Lefix2/pixfrog/docs/img/og-cover.png

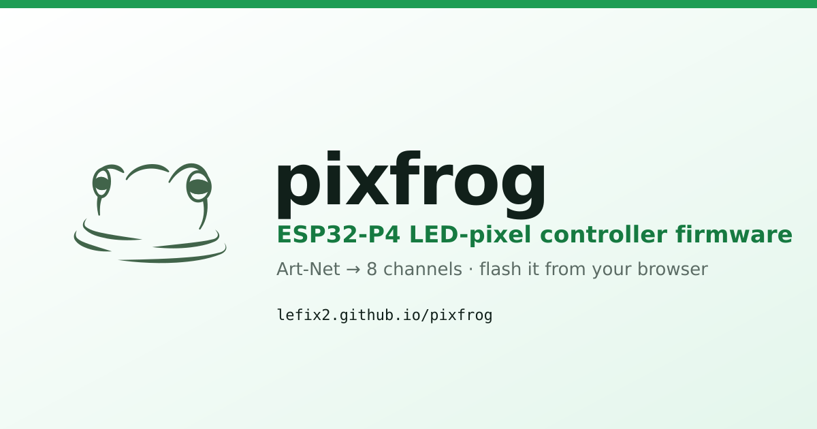
docs/img/og-cover.png
