Lefix2/pixfrog/docs/img/rack-closeup.jpg

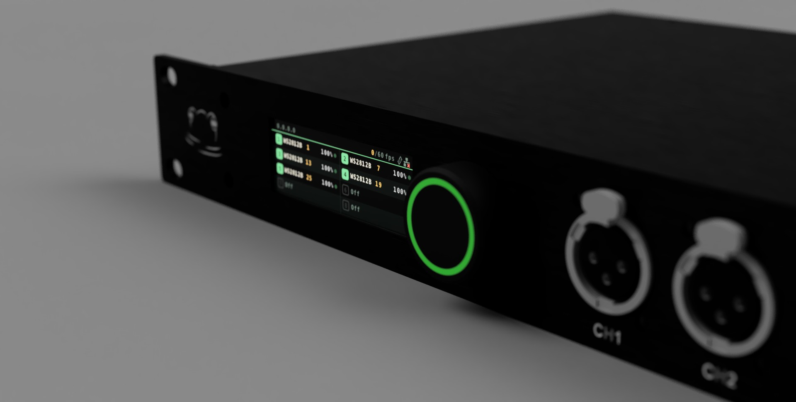
docs/img/rack-closeup.jpg
