Lefix2/pixfrog/docs/img/web-dashboard-fr.png

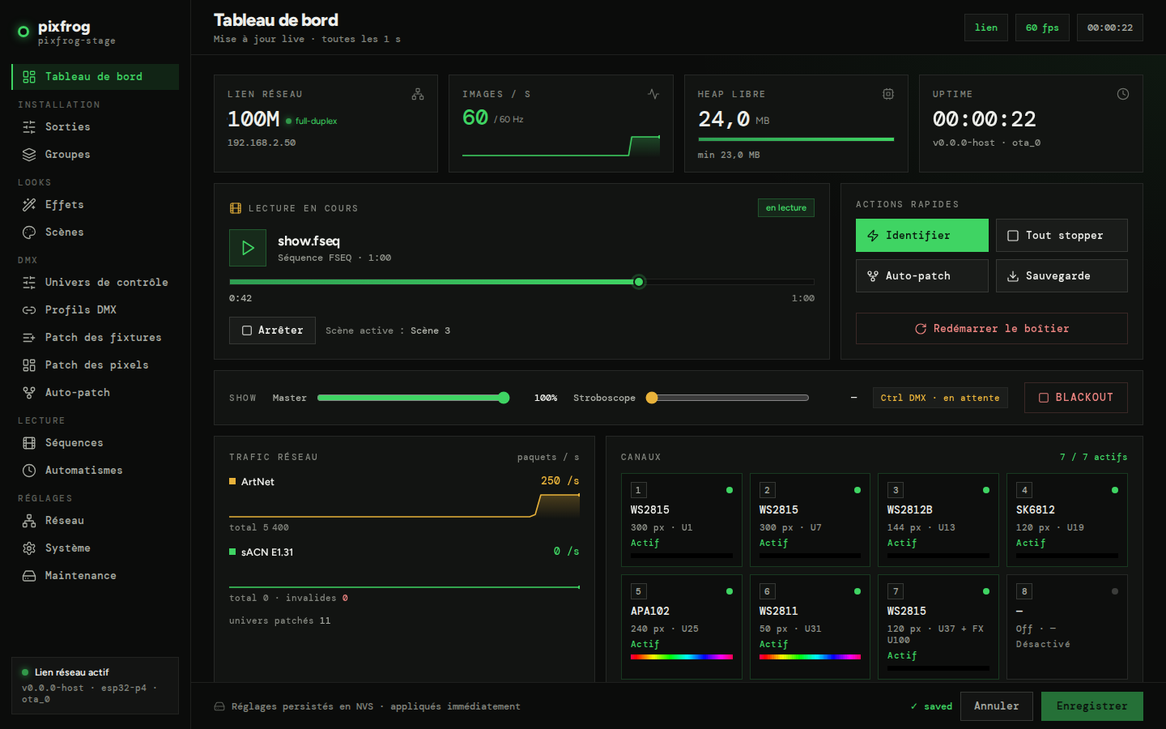
docs/img/web-dashboard-fr.png
