Lefix2/pixfrog/docs/img/web-scenes-fr.png

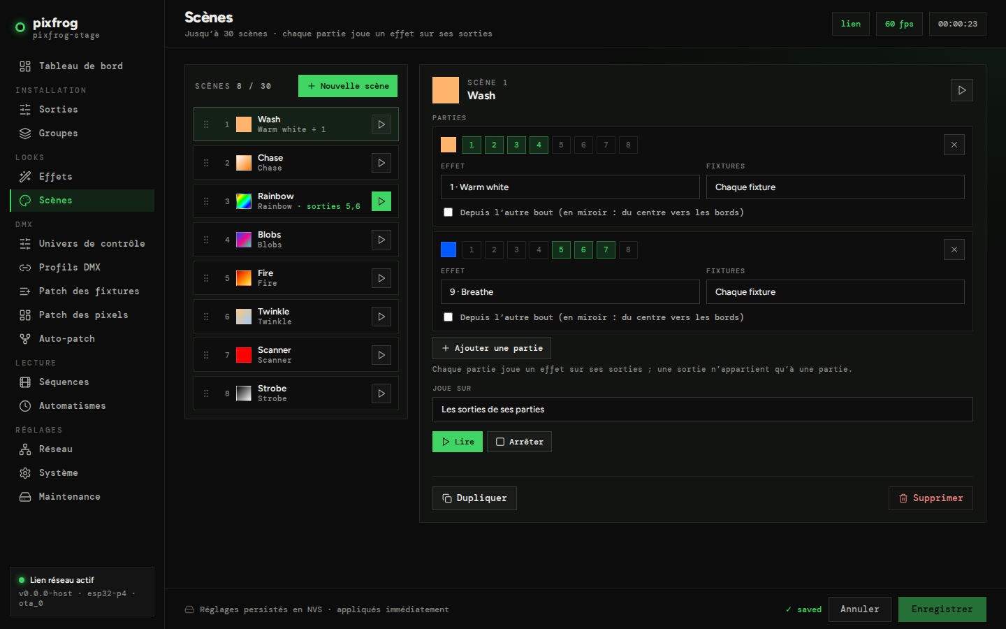
docs/img/web-scenes-fr.png
