Lefix2/pixfrog/tools/emulator/golden/nv3007/channel1.png

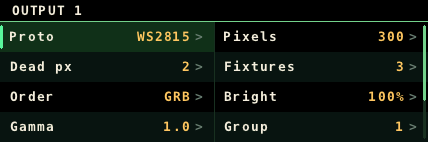
tools/emulator/golden/nv3007/channel1.png
