Lefix2/pixfrog/tools/emulator/golden/nv3007/channel1_dead_px.png

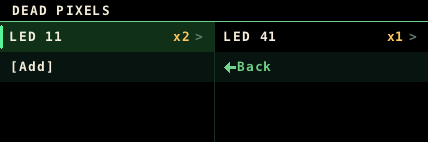
tools/emulator/golden/nv3007/channel1_dead_px.png
