Lefix2/pixfrog/tools/emulator/golden/nv3007/channel1_fixture2.png

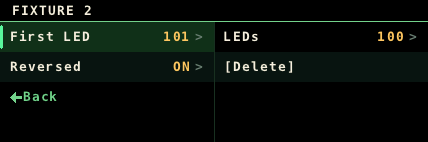
tools/emulator/golden/nv3007/channel1_fixture2.png
