Lefix2/pixfrog/tools/emulator/golden/nv3007/channel1_fixtures.png

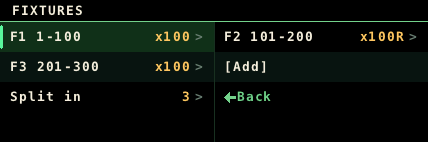
tools/emulator/golden/nv3007/channel1_fixtures.png
