Lefix2/pixfrog/tools/emulator/golden/nv3007/control_menu.png

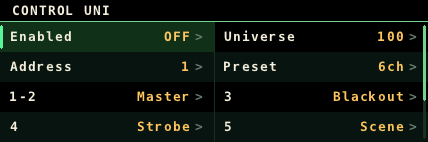
tools/emulator/golden/nv3007/control_menu.png
