Lefix2/pixfrog/tools/emulator/golden/nv3007/dmx_menu.png

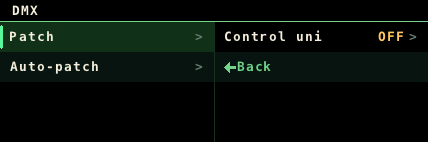
tools/emulator/golden/nv3007/dmx_menu.png
