Lefix2/pixfrog/tools/emulator/golden/nv3007/main_menu.png

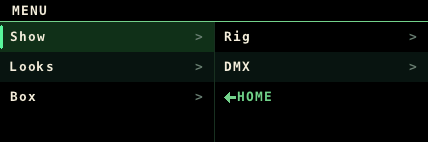
tools/emulator/golden/nv3007/main_menu.png
