Lefix2/pixfrog/tools/emulator/golden/nv3007/output_patch1.png

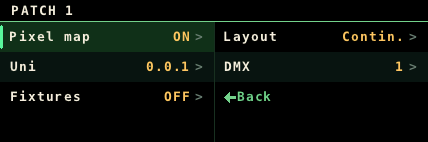
tools/emulator/golden/nv3007/output_patch1.png
