Lefix2/pixfrog/tools/emulator/golden/nv3007/output_patch2.png

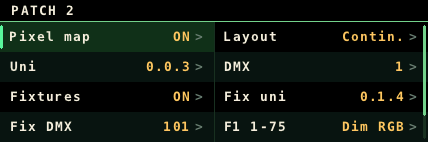
tools/emulator/golden/nv3007/output_patch2.png
