Lefix2/pixfrog/tools/emulator/golden/nv3007/patch_list.png

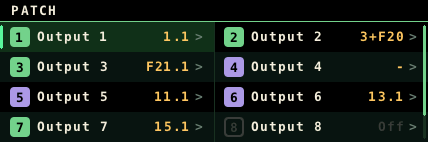
tools/emulator/golden/nv3007/patch_list.png
