Lefix2/pixfrog/tools/emulator/golden/nv3007/rig_menu.png

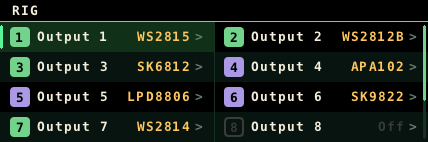
tools/emulator/golden/nv3007/rig_menu.png
