Lefix2/pixfrog/tools/emulator/golden/nv3007/scene_edit.png

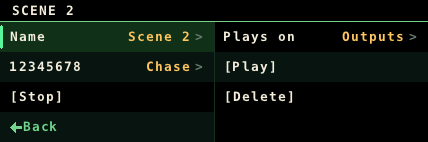
tools/emulator/golden/nv3007/scene_edit.png
