Lefix2/pixfrog/tools/emulator/golden/nv3007/scene_part.png

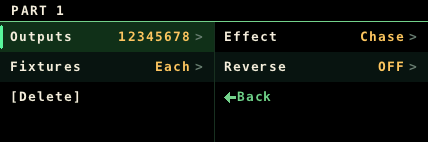
tools/emulator/golden/nv3007/scene_part.png
