Lefix2/pixfrog/tools/emulator/golden/nv3007/scenes_menu.png

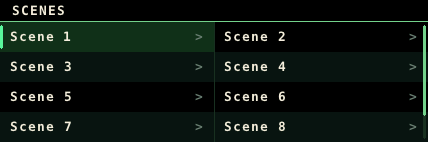
tools/emulator/golden/nv3007/scenes_menu.png
