Lefix2/pixfrog/tools/emulator/golden/nv3007/show_menu.png

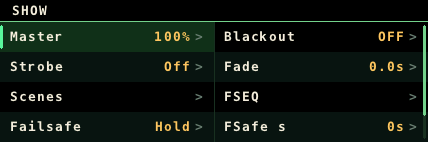
tools/emulator/golden/nv3007/show_menu.png
