Lefix2/pixfrog/tools/emulator/golden/st7789/channel1.png

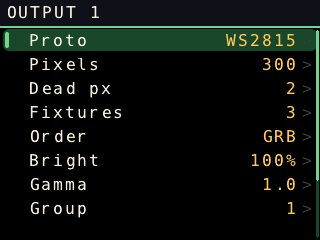
tools/emulator/golden/st7789/channel1.png
