Lefix2/pixfrog/tools/emulator/golden/st7789/channel1_dead_px.png

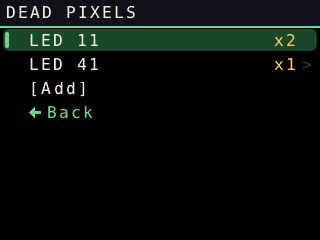
tools/emulator/golden/st7789/channel1_dead_px.png
