Lefix2/pixfrog/tools/emulator/golden/st7789/channel1_fixture2.png

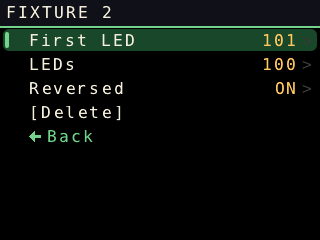
tools/emulator/golden/st7789/channel1_fixture2.png
