Lefix2/pixfrog/tools/emulator/golden/st7789/channel1_fixtures.png

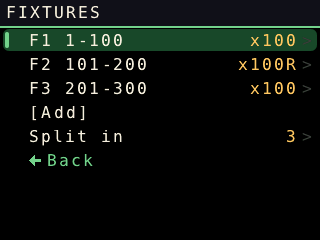
tools/emulator/golden/st7789/channel1_fixtures.png
