Lefix2/pixfrog/tools/emulator/golden/st7789/control_menu.png

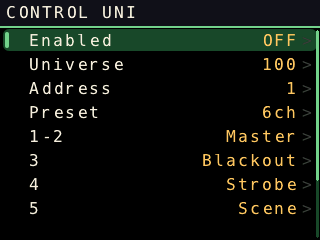
tools/emulator/golden/st7789/control_menu.png
