Lefix2/pixfrog/tools/emulator/golden/st7789/main_menu.png

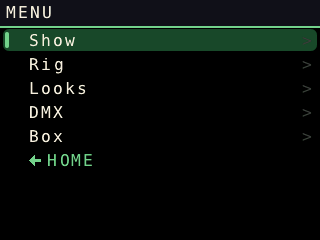
tools/emulator/golden/st7789/main_menu.png
