Lefix2/pixfrog/tools/emulator/golden/st7789/output_patch1.png

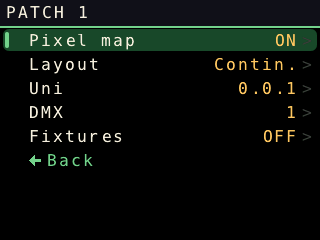
tools/emulator/golden/st7789/output_patch1.png
