Lefix2/pixfrog/tools/emulator/golden/st7789/output_patch2.png

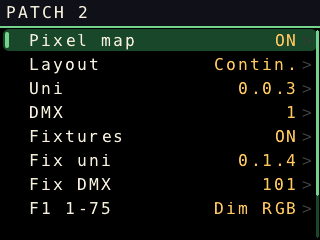
tools/emulator/golden/st7789/output_patch2.png
