Lefix2/pixfrog/tools/emulator/golden/st7789/patch_list.png

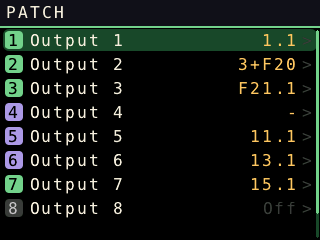
tools/emulator/golden/st7789/patch_list.png
