Lefix2/pixfrog/tools/emulator/golden/st7789/rig_menu.png

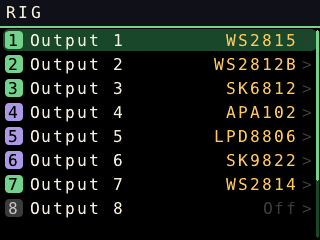
tools/emulator/golden/st7789/rig_menu.png
