Lefix2/pixfrog/tools/emulator/golden/st7789/scene_edit.png

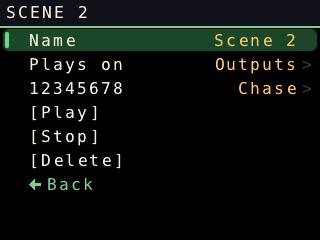
tools/emulator/golden/st7789/scene_edit.png
