Lefix2/pixfrog/tools/emulator/golden/st7789/scene_part.png

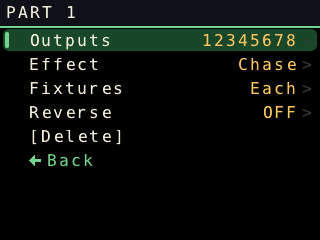
tools/emulator/golden/st7789/scene_part.png
