Lefix2/pixfrog/tools/emulator/golden/st7789/scenes_menu.png

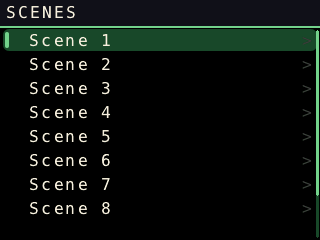
tools/emulator/golden/st7789/scenes_menu.png
