Lefix2/pixfrog/tools/emulator/golden/st7789/show_menu.png

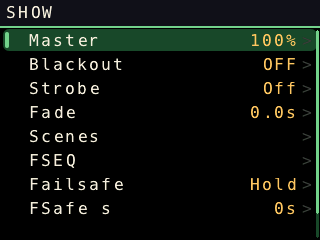
tools/emulator/golden/st7789/show_menu.png
