Lefix2/pixfrog/boards/esp32_p4_devkit.h

// Board definition: Waveshare ESP32-P4 Module DEV-KIT
// (datasheet:
// https://www.espressif.com/sites/default/files/documentation/esp32-p4_datasheet_en.pdf)
//
// Pinout source: Waveshare ESP32-P4 Module DEV-KIT schematic (P6 40-pin header).
// Only GPIOs exposed on P6 are candidates here.
//
// ════════════════════════════════════════════════════════════════════════════
// P6  —  40-pin 2.54 mm header (even = left row, odd = right row)
// ════════════════════════════════════════════════════════════════════════════
//
//   Pin  Left              │  Pin  Right
//   ──────────────────────────────────────
//    2   GPIO7  (I2C SDA)  │   1   VCC_5V
//    4   GPIO8  (I2C SCL)  │   3   GND
//    6   GPIO23 (LED CH3 CLK) │ 5  GPIO37  (UART0 TXD)
//    8   GND               │   7   GPIO38  (UART0 RXD)
//   10   GPIO21 (TFT DC)   │   9   GPIO22  (LED CH3 DATA)
//   12   —                 │  11   GND
//   14   GPIO6  (TFT MOSI) │  13   GPIO5   (LED CH2 CLK)
//   16   —                 │  15   GPIO4   (LED CH2 DATA)
//   18   —                 │  17   GND
//   20   GPIO3  (LED CH1 CLK) │ 19  GPIO1  (status LED)
//   22   GPIO2  (LED CH1 DATA) │ 21  GPIO36 (strapping — keep HIGH)
//   24   GPIO0  (TFT CLK)  │  23   GPIO32  (LED CH6 DATA)
//   26   GND               │  25   GPIO25  (LED CH4 CLK)
//   28   GPIO24 (LED CH4 DATA) │ 27  GND
//   30   GPIO33 (LED CH6 CLK) │ 29  GPIO54  (LED CH8 CLK)
//   32   GPIO26 (LED CH5 DATA) │ 31  GND
//   34   GPIO48 (LED CH7 CLK) │ 33  GPIO46  (LED CH5 CLK)
//   36   GPIO53 (LED CH8 DATA) │ 35  GPIO27  (TFT RST)
//   38   GPIO47 (LED CH7 DATA) │ 37  GPIO45  (TFT backlight)
//   40   GND               │  39   —
//
// ════════════════════════════════════════════════════════════════════════════
// On-board peripheral  →  GPIO usage
// ════════════════════════════════════════════════════════════════════════════
//
//  LED bus (LCD_CAM 16-bit parallel, 16 MHz PCLK)
//    CH1 DATA/CLK : GPIO2  / GPIO3
//    CH2 DATA/CLK : GPIO4  / GPIO5
//    CH3 DATA/CLK : GPIO22 / GPIO23
//    CH4 DATA/CLK : GPIO24 / GPIO25
//    CH5 DATA/CLK : GPIO26 / GPIO46
//    CH6 DATA/CLK : GPIO32 / GPIO33
//    CH7 DATA/CLK : GPIO47 / GPIO48
//    CH8 DATA/CLK : GPIO53 / GPIO54
//
//  I2C shared bus (OLED SSD1306 + seesaw encoder)
//    SDA : GPIO7    SCL : GPIO8
//
//  SPI display (ST7789V / ILI9341) — on the shield's J13 break-out header
//    CLK  : GPIO0    MOSI : GPIO6
//    CS   : GPIO20   DC   : GPIO21
//    RST  : GPIO27
//
//  Status LED         : GPIO1
//  UART0 console      : TX=GPIO37  RX=GPIO38
//
//  Ethernet RMII (IP101GR PHY, fixed SoC pins — not on P6)
//    TXD0=34  TXD1=35  TX_EN=49  RXD0=29  RXD1=30  CRS_DV=28  REF_CLK=50
//    MDC=31   MDIO=52  PHY_RESET=51
//
//  ES8311 audio codec + NS4150B speaker amp (on-board, not on J13)
//    MCLK=GPIO13  SCLK=GPIO12  LRCK=GPIO10  ASDOUT(codec→P4)=GPIO11
//    DSDIN(P4→codec)=GPIO9. Config via the shared I2C bus above (0x18).
//    Amp enable PA_CTRL: R52 removed, 10 kΩ pull-up to 3.3 V (GPIO53 is
//    LED CH8 DATA only).
//
// ════════════════════════════════════════════════════════════════════════════
// Strapping pins (ESP32-P4 datasheet §3.3)
// ════════════════════════════════════════════════════════════════════════════
//
//  GPIO35 — boot/download select (driven by BOOT button, not on P6)
//  GPIO36 — must read HIGH for reliable serial-download boot
//  GPIO34 — JTAG source select at boot
//
// GPIO matrix: every peripheral signal is routed through the GPIO matrix,
// so any free GPIO is a valid LCD_CAM data line or SPI pin. The only
// hard constraints are the strapping pins above and the fixed RMII pins.

#pragma once

#include <stdint.h>

namespace pixfrog::board {

// ────────────────────────────────────────────────────────────────────────────
// Identification
// ────────────────────────────────────────────────────────────────────────────

constexpr const char* kBoardName = "esp32_p4_devkit";
constexpr const char* kBoardRev  = "v0";

// ────────────────────────────────────────────────────────────────────────────
// LCD_CAM 16-bit parallel — DATA[k] and CLOCK[k] for 8 LED channels
// ────────────────────────────────────────────────────────────────────────────
//
// Bit position on the parallel bus → physical GPIO.
// Bit 0 = CH1 DATA, Bit 1 = CH1 CLOCK, Bit 2 = CH2 DATA, etc.
//
// Pad power domains (P4 datasheet §2, Waveshare module wiring):
//   GPIO 2-25   VDD_IO_0/4 ← 3.3 V direct
//   GPIO 39-48  VDD_IO_5   ← internal LDO VO4 — MUST be programmed to 3.3 V
//               at boot (main::power_vdd_io5_pads), else outputs swing ~1.2 V.
//               Covers CH5 CLOCK (46) and CH7 DATA/CLOCK (47/48).
//   GPIO 49-54  VDD_IO_6   ← 3.3 V direct

constexpr int kLedDataGpio[8]  = { 2, 4, 22, 24, 26, 32, 47, 53 };
constexpr int kLedClockGpio[8] = { 3, 5, 23, 25, 46, 33, 48, 54 };

// Full 16-pin bus in bit order (DATA0, CLK0, DATA1, CLK1, ...).
// clang-format off
constexpr int kLedBusGpio[16] = {
     2,  3,   4,  5,  22, 23,  24, 25,
    26, 46,  32, 33,  47, 48,  53, 54,
};
// clang-format on

// ────────────────────────────────────────────────────────────────────────────
// Ethernet — RMII to on-board IP101GRI PHY
// ────────────────────────────────────────────────────────────────────────────
//
// Verified against the Waveshare DEV-KIT schematic (PHY U7 = IP101GRI) and
// the official board pinout. The PHY's RMII + management pins use fixed SoC
// GPIOs (28-35, 49-52) and PHY RESET is GPIO51; none are on the P6 header,
// so they do not constrain the LED pinout above.
//
// RMII data/clock equal the ESP32-P4 ETH_ESP32_EMAC_DEFAULT_CONFIG() defaults
// (IDF v5.5), so main/init_network() only has to override MDC/MDIO:
//   TXD0=34  TXD1=35  TX_EN=49  RXD0=29  RXD1=30  CRS_DV=28  REF_CLK(50M)=50
//
// Management bus + reset are read straight off U7:
//   MDC = pin 22, MDIO = pin 23, RESET = pin 32.

constexpr int kEthMdcGpio      = 31;
constexpr int kEthMdioGpio     = 52;
constexpr int kEthPhyResetGpio = 51;    // drive HIGH to release U7 from reset
constexpr int kEthPhyAddress   = 0x01;  // IP101GRI strap (AD0/AD3); verify if link fails

// ────────────────────────────────────────────────────────────────────────────
// I2C — shared bus for OLED + seesaw encoder
// ────────────────────────────────────────────────────────────────────────────

constexpr int kI2cPort        = 0;
constexpr int kI2cSdaGpio     = 7;  // header pin SDA(GPIO7)
constexpr int kI2cSclGpio     = 8;  // header pin SCL(GPIO8)
constexpr uint32_t kI2cFreqHz = 400'000;

constexpr uint8_t kOledI2cAddr    = 0x3C;
constexpr uint8_t kEncoderI2cAddr = 0x36;  // Adafruit seesaw 4991 default
// Encoder INT_N is deliberately not wired: the firmware time-polls the seesaw
// at ~30 Hz, so a 4-wire I2C harness (VCC/GND/SDA/SCL) is sufficient and
// GPIO 21 stays free.

// ────────────────────────────────────────────────────────────────────────────
// SPI display — ST7789V or ILI9341
// ────────────────────────────────────────────────────────────────────────────
//
// Routed to the shield's J13 break-out header. The ES8311 codec I2S pins
// (GPIO9-13) the display used to share are NOT exposed on J13, so the SPI
// display moved to the free, 3.3 V-direct, non-strapping GPIOs available
// there: 0/6/20/21/27. J13 also exposes GPIO36 (now the backlight, below) and
// GPIO45, which is NOT free: it gates the microSD supply (see kSdPowerGpio).
// SPI2 (HSPI) is used; every signal is routed through the GPIO matrix so any
// free GPIO is valid.

constexpr int kDisplaySpiHost  = 1;  // SPI2 / HSPI
constexpr int kDisplayClkGpio  = 0;
constexpr int kDisplayMosiGpio = 6;
constexpr int kDisplayCsGpio   = 20;
constexpr int kDisplayDcGpio   = 21;
constexpr int kDisplayRstGpio  = 27;
// 20 MHz: the P4's default SPI clock source can't derive 40 MHz cleanly
// (spi_bus_add_device → "invalid sclk speed"); 20 MHz is a clean divisor and
// well within the GPIO-matrix routing limit. Plenty for the 320×240 panel.
constexpr uint32_t kDisplaySpiFreqHz = 20'000'000;

// Backlight enable (LEDC PWM), on J13's GPIO36. Off from boot, raised only
// once the first UI frame has been pushed, so the panel never shows its white
// power-on state. -1 disables backlight control (BL hard-wired on).
// GPIO36 is a boot strapping pin, but the boot mode is decided by GPIO35 (the
// BOOT button, pulled high: flash boot); GPIO36 only matters with BOOT held,
// for the download modes. It was on GPIO45 until the microSD showed that pin
// gates the card supply: lighting the panel switched the card off.
constexpr int kDisplayBacklightGpio = 36;

// ────────────────────────────────────────────────────────────────────────────
// Miscellaneous
// ────────────────────────────────────────────────────────────────────────────

// ────────────────────────────────────────────────────────────────────────────
// microSD — SDMMC 4-bit (GPIO39-44, VDD_IO_5 domain = LDO VO4 @ 3.3 V)
// ────────────────────────────────────────────────────────────────────────────
//
// GPIO39-44 are in the VDD_IO_5 pad domain, powered by the same LDO VO4
// that is programmed to 3.3 V by power_vdd_io5_pads() at boot.
// None of these GPIOs appear in the LED bus, SPI display, I2C, ETH, or UART
// pin lists, so they are freely available for the SD slot.

// Per the DEV-KIT schematic (MicroSD block, TF slot SD1): the data lines do
// not follow the GPIO order — D0/D1 are 39/40, D2/D3 41/42, CLK 43, CMD 44.
// (The previous 39..44 = CLK, CMD, D0..D3 mapping never reached a card.)
constexpr int kSdmmcClkGpio = 43;
constexpr int kSdmmcCmdGpio = 44;
constexpr int kSdmmcD0Gpio  = 39;
constexpr int kSdmmcD1Gpio  = 40;
constexpr int kSdmmcD2Gpio  = 41;
constexpr int kSdmmcD3Gpio  = 42;

// The card supply goes through P-MOSFET Q1 (AO3401) from LDO VO4, gate on
// GPIO45 with a 10 k pull-down: the card is powered while GPIO45 is LOW.
// fseq::init drives it low before the first mount.
constexpr int kSdPowerGpio = 45;  // active low

// ────────────────────────────────────────────────────────────────────────────
// Miscellaneous
// ────────────────────────────────────────────────────────────────────────────

// ────────────────────────────────────────────────────────────────────────────
// Audio — ES8311 codec over I2S (on-board), config on the shared I2C bus
// ────────────────────────────────────────────────────────────────────────────
// The NS4150B amplifier's enable (PA_CTRL) came from GPIO53 through R52, the
// same pin as LED CH8 DATA: every LED frame toggled the amp. On the bench
// board R52 is removed and PA_CTRL pulled up (10 kΩ to 3.3 V): the amp is
// always on, the firmware mutes the codec when idle (docs/HARDWARE.md §2.7).

// Read once at boot, before the LED outputs: high = R52 removed (main.cpp).
constexpr int kAmpProbeGpio = 53;

constexpr uint16_t kCodecI2cAddr = 0x18;
constexpr int kI2sMclkGpio       = 13;
constexpr int kI2sBclkGpio       = 12;
constexpr int kI2sWsGpio         = 10;
constexpr int kI2sDoutGpio       = 9;   // to the codec's DSDIN (DAC)
constexpr int kI2sDinGpio        = 11;  // from the codec's ASDOUT (ADC)

constexpr int kStatusLedGpio = 1;

// UART0 console (TXD/RXD) is on the dedicated pins GPIO 37 / GPIO 38
// printed on the header silkscreen. Configured by the IDF default
// console driver — not used directly from this board file.
constexpr int kDebugTxGpio = 37;
constexpr int kDebugRxGpio = 38;

}  // namespace pixfrog::board
