Lefix2/pixfrog/components/led_protocols/include/led_protocols.h

// led_protocols — per-protocol pixel-to-DMA-samples encoders.
//
// This component is the pure compute core: given a pixel buffer, a protocol
// descriptor, and a target sample buffer, it emits the parallel-bus 16-bit
// samples that drive the 16-bit LED bus (PARLIO TX by default, or the legacy
// LCD_CAM RGB backend — see led_output).
//
// It has no IDF or hardware dependency and is unit-testable on a host.
//
// See docs/PROTOCOLS.md for timing tables and PCLK derivation.

#pragma once

#include <stddef.h>
#include <stdint.h>

namespace pixfrog::led {

// ────────────────────────────────────────────────────────────────────────────
// Protocol enumeration
// ────────────────────────────────────────────────────────────────────────────

enum class Protocol : uint8_t {
    // Channel disabled: no output is emitted, no universes are consumed, and the
    // UI hides every per-channel setting. First (= 0) so it is both the default
    // for a fresh channel and the first entry in the protocol picker.
    Off     = 0,
    WS2815  = 1,
    WS2812B = 2,
    WS2811  = 3,
    SK6812  = 4,
    WS2814  = 5,
    APA102  = 6,
    SK9822  = 7,
    LPD8806 = 8,
    // 9 was DMX512 output — moved to the DMX node firmware (a fork). NVS blobs
    // holding 9 load as Off (config::sanitize_channel).
    COUNT,
};

// A disabled channel: produces no DMA samples and claims no universes.
constexpr bool is_off(Protocol p) {
    return p == Protocol::Off;
}

constexpr bool is_clocked(Protocol p) {
    return p == Protocol::APA102 || p == Protocol::SK9822 || p == Protocol::LPD8806;
}

constexpr bool is_rgbw(Protocol p) {
    return p == Protocol::SK6812 || p == Protocol::WS2814;
}

// Source bytes per pixel. A disabled channel maps to 0 bytes so it consumes
// neither buffer nor universe.
constexpr size_t bytes_per_pixel(Protocol p) {
    if (is_off(p)) return 0;
    return is_rgbw(p) ? 4 : 3;
}

// ────────────────────────────────────────────────────────────────────────────
// Color order
// ────────────────────────────────────────────────────────────────────────────

enum class ColorOrder : uint8_t {
    // RGB permutations (3-colour strips). The W byte, when the protocol has one,
    // is always appended last by apply_order.
    RGB,
    RBG,
    GRB,
    GBR,
    BRG,
    BGR,
    // RGBW strips: W last or first, with the six RGB orders. RGBW and GRBW keep
    // their stored values (6, 7); the others follow.
    RGBW,
    GRBW,
    RBGW,
    GBRW,
    BRGW,
    BGRW,
    WRGB,
    WRBG,
    WGRB,
    WGBR,
    WBRG,
    WBGR,
    COUNT,
};

// Names in ColorOrder order — the web, the console and the menus all read
// them here. A strip's wire order: position k carries the channel named by
// its k-th letter (a 3-letter order sends W, if any, last).
inline constexpr const char* kColorOrderNames[] = {
    "RGB",  "RBG",  "GRB",  "GBR",  "BRG",  "BGR",  "RGBW", "GRBW", "RBGW",
    "GBRW", "BRGW", "BGRW", "WRGB", "WRBG", "WGRB", "WGBR", "WBRG", "WBGR",
};
static_assert(sizeof(kColorOrderNames) / sizeof(kColorOrderNames[0]) ==
                  static_cast<size_t>(ColorOrder::COUNT),
              "one name per colour order");

// The first order that names W: the orders a 4-channel strip takes.
constexpr ColorOrder kFirstRgbwOrder = ColorOrder::RGBW;

inline const char* color_order_name(ColorOrder o) {
    const auto i = static_cast<size_t>(o);
    return i < static_cast<size_t>(ColorOrder::COUNT) ? kColorOrderNames[i] : "?";
}

// ────────────────────────────────────────────────────────────────────────────
// Timing — derived from f_PCLK (cf. docs/PROTOCOLS.md §3)
// ────────────────────────────────────────────────────────────────────────────

// PCLK frequency the 16-bit LED bus is configured at, system-wide (both the
// PARLIO TX and LCD_CAM backends clock at this rate).
// Changing this requires recomputing every Timing::samples_* constant.
constexpr uint32_t kPclkHz = 16'000'000;

// Worst-case sample count for one frame, used to size the PSRAM frame buffer.
// 1024 px × 32 bits (RGBW) × 40 samples (WS2811-slow) + 4480 (TRESET).
// At 2 bytes per sample, this gives ~2.6 MB per FB (PARLIO keeps three,
// the legacy LCD_CAM backend two). Buffers are sized to the frame actually
// configured, so this is a ceiling, not the steady-state footprint.
constexpr uint32_t kMaxPixelsPerChannel = 1024;
constexpr uint32_t kMaxBitsPerPixel     = 32;
constexpr uint32_t kMaxSamplesPerBit    = 40;
constexpr uint32_t kMaxResetSamples     = 4480;
constexpr uint32_t kMaxSamplesPerFrame  = kMaxPixelsPerChannel * kMaxBitsPerPixel *
                                             kMaxSamplesPerBit +
                                         kMaxResetSamples;

// Bounds on a clocked-SPI channel's requested bit clock.
//
// The floor is not a matter of taste. timing_for() turns the request into
// kPclkHz/clock samples per bit-clock, so a slow clock inflates the frame
// instead of shortening it: at kMaxPixelsPerChannel an APA102 frame is
// 4 + 4×1024 + 65 = 4165 bytes, i.e. 33320 samples per sample-per-clock. Below
// roughly 410 kHz that crosses kMaxSamplesPerFrame, the output backend refuses
// the frame, and the channel goes dark while logging once per frame — a config
// value that silently disables an output. 500 kHz keeps the worst case at
// 1066240 samples, well under the cap, and is already far slower than any
// APA102/LPD8806 strip needs. test_led_protocols pins this.
constexpr uint32_t kMinClockHz = 500'000;
constexpr uint32_t kMaxClockHz = kPclkHz / 2;

// Samples per logical "thing" — varies by protocol family.
struct Timing {
    // For 1-wire NRZ: samples high to encode '0' and '1', total samples per bit.
    uint16_t samples_t0h;
    uint16_t samples_t1h;
    uint16_t samples_bit;  // = T0H + T0L = T1H + T1L (within ±1 sample)

    // For clocked SPI-like: samples per full CLOCK cycle (must be even, ≥ 2).
    uint16_t samples_per_clock;

    // Frame-reset samples to keep DATA low after the last bit (latches the strip).
    uint32_t samples_reset;
};

// Returns a baked-in timing for the given protocol at compile time.
// `requested_clock_hz` is used only for clocked protocols and clamped to PCLK/2.
Timing timing_for(Protocol p, uint32_t requested_clock_hz = 4'000'000);

// ────────────────────────────────────────────────────────────────────────────
// Channel descriptor for the encoder
// ────────────────────────────────────────────────────────────────────────────

// Per-component 8-bit lookup tables: gamma correction + white balance,
// applied to the SOURCE components (before colour-order mapping). Built by
// build_pixel_lut(); a null pointer in ChannelDesc skips the lookup.
struct PixelLut {
    uint8_t r[256];
    uint8_t g[256];
    uint8_t b[256];
    uint8_t w[256];  // gamma only — white balance has no meaning on the W die
};

// gamma_x10: 10 = linear (identity), 22 = gamma 2.2, clamped to [10, 40].
// wb_*: 255 = unity gain, 0 is treated as 255 (zero-fill migration safety).
void build_pixel_lut(PixelLut& lut, uint8_t gamma_x10, uint8_t wb_r, uint8_t wb_g, uint8_t wb_b);

// ────────────────────────────────────────────────────────────────────────────
// Pixel gaps — dead physical pixels inside a line
// ────────────────────────────────────────────────────────────────────────────

// A run of physical LEDs that carry no data: a sacrificial level-shift pixel at
// the head of a line, or a repeater / injector with an LED chip mid-line. Gaps
// are wiring, so they are indexed in physical (controller-side) order and never
// move with invert or grouping. Live pixels fill the positions around them.
constexpr size_t kMaxPixelGaps = 8;

struct PixelGap {
    uint16_t pos;  // first dead physical pixel, 0-based
    uint16_t len;  // 0 = unused slot
};

// Sorts by position, merges overlapping/adjacent runs and packs the used gaps
// first (unused slots zeroed). Returns the number of gaps in use.
inline size_t normalize_gaps(PixelGap* g, size_t n) {
    size_t used = 0;
    for (size_t i = 0; i < n; ++i)
        if (g[i].len) g[used++] = g[i];
    for (size_t i = 1; i < used; ++i)
        for (size_t j = i; j > 0 && g[j].pos < g[j - 1].pos; --j) {
            const PixelGap t = g[j];
            g[j]             = g[j - 1];
            g[j - 1]         = t;
        }
    size_t out = 0;
    for (size_t i = 0; i < used; ++i) {
        const uint32_t end = static_cast<uint32_t>(g[i].pos) + g[i].len;
        if (out && g[i].pos <= static_cast<uint32_t>(g[out - 1].pos) + g[out - 1].len) {
            const uint32_t prev_end = static_cast<uint32_t>(g[out - 1].pos) + g[out - 1].len;
            if (end > prev_end) g[out - 1].len = static_cast<uint16_t>(end - g[out - 1].pos);
        } else {
            g[out++] = g[i];
        }
    }
    for (size_t i = out; i < n; ++i)
        g[i] = PixelGap{ 0, 0 };
    return out;
}

// Number of gaps in use in a normalized array (they are packed first).
inline size_t gap_count(const PixelGap* g, size_t n) {
    size_t k = 0;
    while (k < n && g[k].len)
        ++k;
    return k;
}

// Physical pixels a line of `live` live pixels spans: every gap that starts
// before the end of the line (as extended by the gaps before it) is inside it.
inline uint32_t physical_count(uint32_t live, const PixelGap* g, size_t n) {
    uint32_t phys = live;
    for (size_t i = 0; i < n && g[i].len; ++i) {
        if (g[i].pos >= phys) break;
        phys += g[i].len;
    }
    return phys;
}

// Live pixels among the first `phys` physical positions.
inline uint32_t live_within(uint32_t phys, const PixelGap* g, size_t n) {
    uint32_t dead = 0;
    for (size_t i = 0; i < n && g[i].len; ++i) {
        if (g[i].pos >= phys) break;
        const uint32_t end  = static_cast<uint32_t>(g[i].pos) + g[i].len;
        dead               += (end < phys ? end : phys) - g[i].pos;
    }
    return phys - dead;
}

// Live index of physical position `p`, or -1 when it falls in a gap.
inline int32_t live_index(uint32_t p, const PixelGap* g, size_t n) {
    uint32_t dead_before = 0;
    for (size_t i = 0; i < n && g[i].len; ++i) {
        if (p < g[i].pos) break;
        if (p < static_cast<uint32_t>(g[i].pos) + g[i].len) return -1;
        dead_before += g[i].len;
    }
    return static_cast<int32_t>(p - dead_before);
}

struct ChannelDesc {
    Protocol protocol;
    ColorOrder color_order;
    uint16_t pixel_count;  // physical pixels on the wire (live + dead, see gaps)
    uint8_t brightness;    // 0..255, applied at encode time
    uint8_t grouping;      // 1..8; N source pixels share one output pixel
    bool invert_direction;
    uint8_t bus_bit_data;           // which bit of the 16-bit bus carries DATA   (0..15)
    uint8_t bus_bit_clock;          // which bit carries CLOCK (clocked protocols only)
    uint32_t clock_hz;              // requested CLOCK rate (clocked only)
    const PixelLut* lut = nullptr;  // optional gamma/white-balance LUT
    // Normalized dead-pixel runs (null = none). The source buffer then holds
    // live_within(pixel_count) pixels; dead positions are emitted black.
    const PixelGap* gaps = nullptr;
    uint8_t gap_count    = 0;
};

// ────────────────────────────────────────────────────────────────────────────
// Encoder entry point
// ────────────────────────────────────────────────────────────────────────────

// Encode `pixels` (length = pixel_count × bytes_per_pixel) into `out_samples`
// using the channel's protocol. `out_samples` must be at least
// `encoded_size_samples(desc)` words wide. Existing bits in `out_samples`
// outside this channel's bus_bit_data/bus_bit_clock are preserved (OR-ed),
// allowing 8 channels to share the same DMA buffer.
//
// Returns the number of samples actually written.
size_t encode_channel(const ChannelDesc& desc, const uint8_t* pixels, uint16_t* out_samples,
                      size_t out_samples_capacity);

// Worst-case sample count for `desc`, used for buffer sizing.
size_t encoded_size_samples(const ChannelDesc& desc);

// Encode every channel of one frame in a single traversal of `out_samples`.
//
// Unlike per-channel encode_channel calls (read-modify-write over the whole
// frame region, once per channel), the NRZ channels are merged and written
// with pure stores — `out_samples` needs NO pre-zeroing and [0, return value)
// is fully initialized on return. Clocked SPI channels are OR-ed
// on top. Off channels and null pixel pointers are skipped.
//
// `descs` / `pixels` are parallel arrays of `channel_count` entries.
// Returns the frame length in samples (max over channels, incl. reset tails),
// or 0 if there is nothing to emit or the capacity is too small.
size_t encode_frame(const ChannelDesc* descs, const uint8_t* const* pixels, size_t channel_count,
                    uint16_t* out_samples, size_t out_samples_capacity);

}  // namespace pixfrog::led
